kyemacdonald/HA-Smart-Pucks/images/PXL_20260608_213057716.jpg

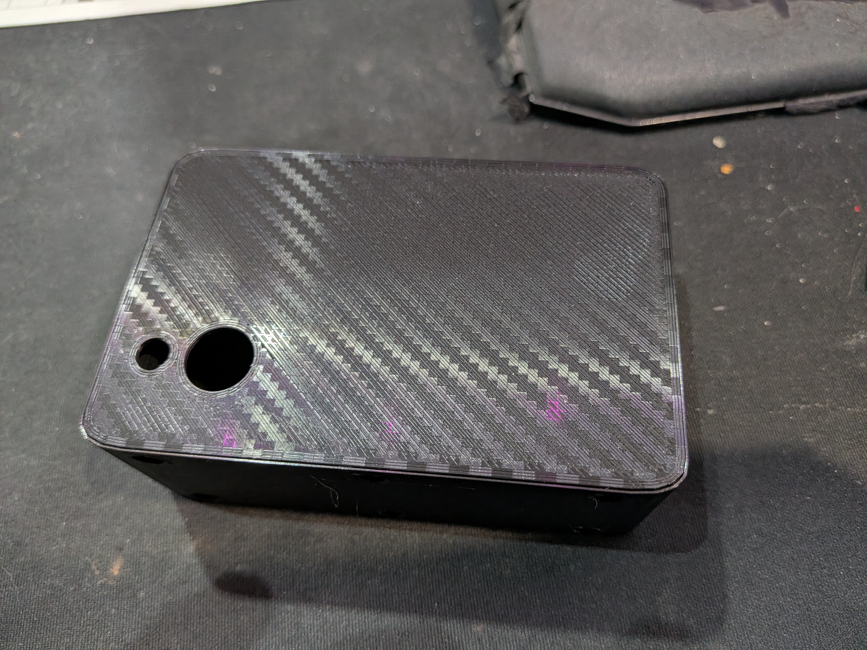
images/PXL_20260608_213057716.jpg
