kyemacdonald/HA-Smart-Pucks/images/PXL_20260608_213158371.jpg

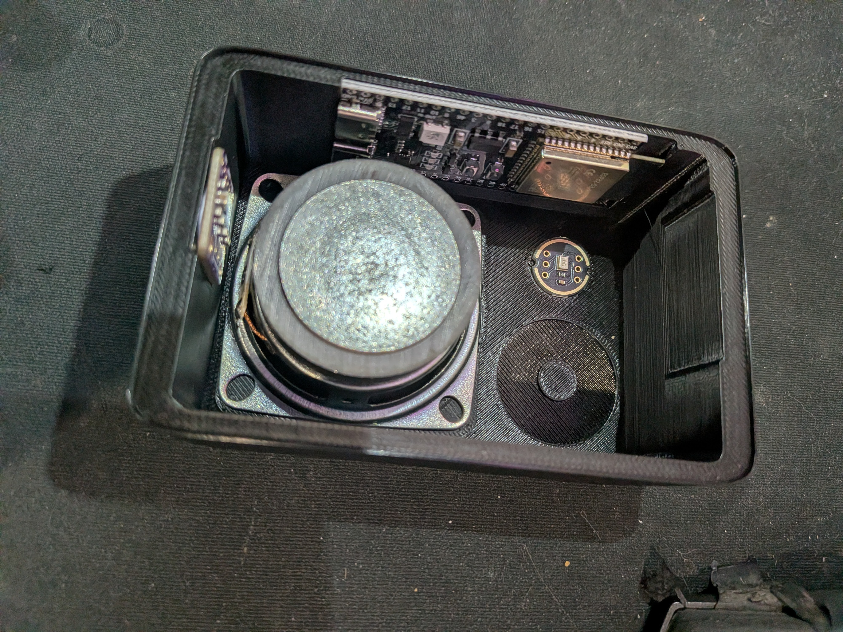
images/PXL_20260608_213158371.jpg
