kyemacdonald/HA-Smart-Pucks/images/PXL_20260609_092001501.jpg

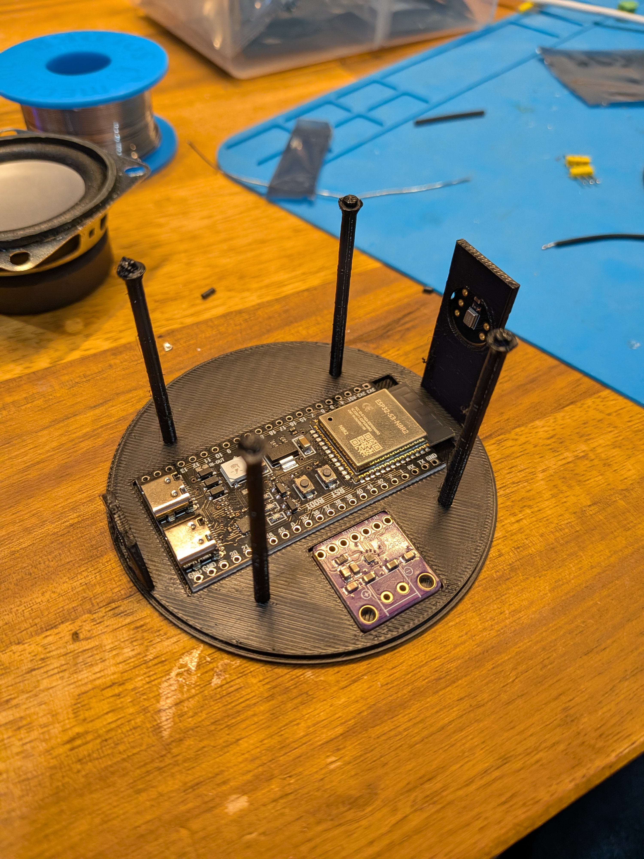
images/PXL_20260609_092001501.jpg
