kyemacdonald/HA-Smart-Pucks/images/PXL_20260609_092006840.jpg

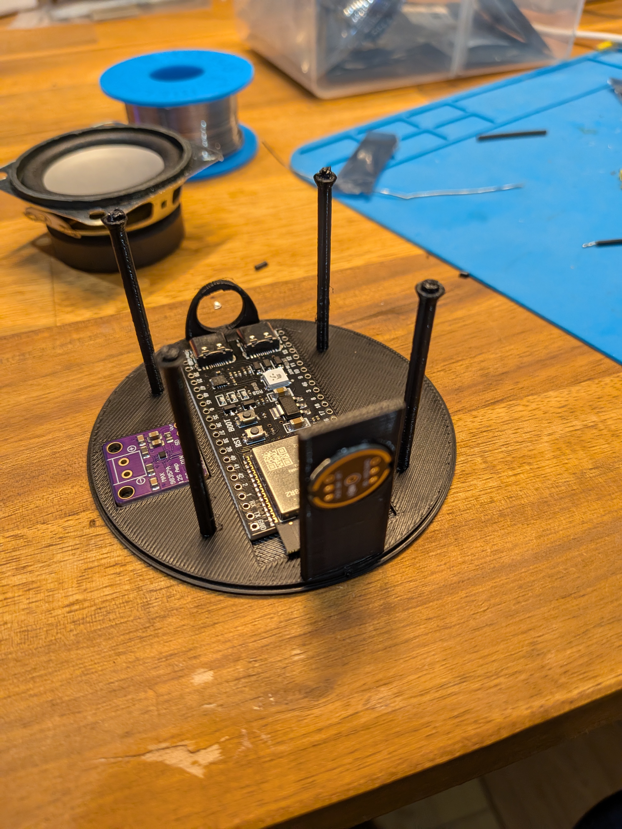
images/PXL_20260609_092006840.jpg
