kyemacdonald/HA-Smart-Pucks/images/PXL_20260609_092016563.jpg

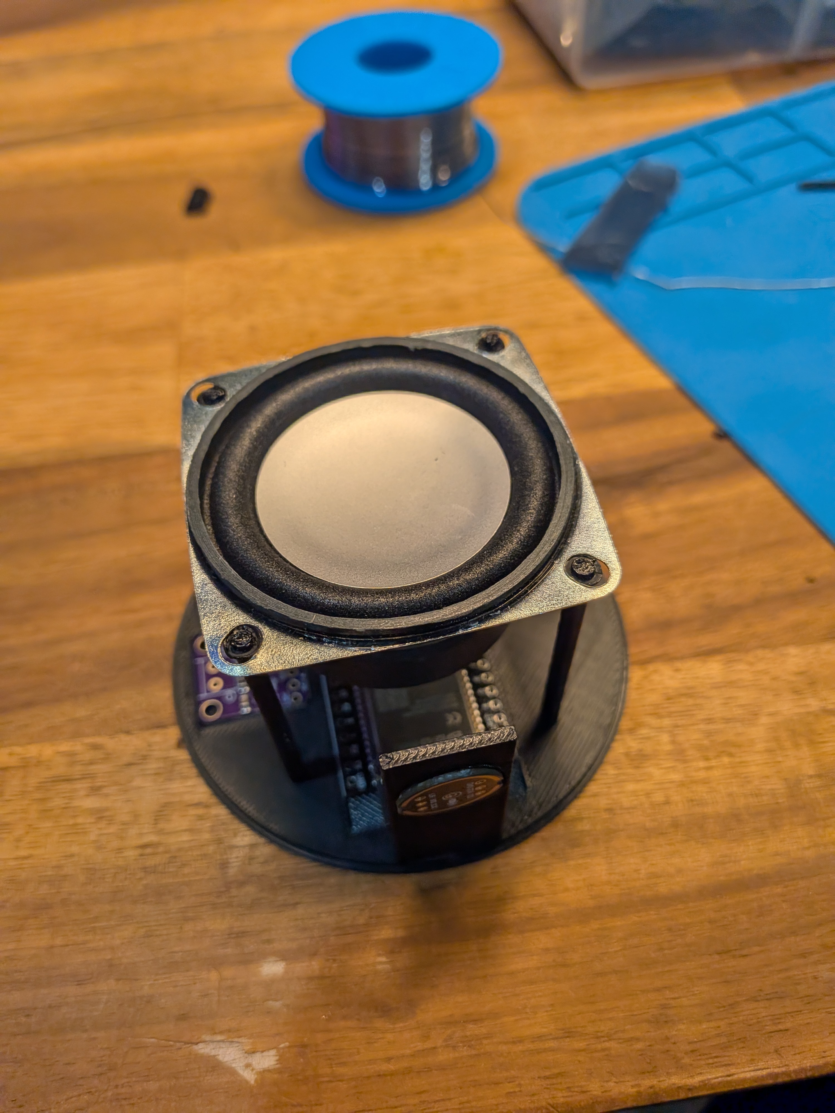
images/PXL_20260609_092016563.jpg
